monoKeith/GPS_Performance_Box/Firmware/src/monitor.cpp

/**
   The MIT License (MIT)

   Copyright (c) 2018 by ThingPulse, Daniel Eichhorn
   Copyright (c) 2018 by Fabrice Weinberg

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
   ThingPulse invests considerable time and money to develop these open source libraries.
   Please support us by buying our products (and not the clones) from
   https://thingpulse.com

*/

#include "monitor.h"

namespace monitor
{

    SSD1306Wire display = SSD1306Wire(0x3c, SDA_PIN, SCL_PIN);

    void setup()
    {
        display.init();
        display.flipScreenVertically();
    }

    void drawBootScreen()
    {
        // Clear
        display.clear();
        // Draw
        display.setFont(Roboto_Mono_Medium_18);
        display.setTextAlignment(TEXT_ALIGN_LEFT);
        display.drawString(0, 0, "GPS");
        display.setFont(Roboto_Mono_Medium_15);
        display.setTextAlignment(TEXT_ALIGN_RIGHT);
        display.drawString(128, 20, "Speedometer");
        display.setFont(ArialMT_Plain_10);
        display.setTextAlignment(TEXT_ALIGN_CENTER);
        display.drawString(64, 35, "Initializing...");
        display.setTextAlignment(TEXT_ALIGN_RIGHT);
        display.drawString(128, 50, "BY KEITH");
        // Done
        display.display();
    }

    void drawDebugScreen()
    {
        // Clear
        display.clear();

        // Clock
        display.setFont(ArialMT_Plain_16);
        display.setTextAlignment(TEXT_ALIGN_LEFT);
        display.drawString(0, 0, state::displayTime);
        // Date
        display.setFont(ArialMT_Plain_10);
        display.setTextAlignment(TEXT_ALIGN_RIGHT);
        display.drawString(128, 6, state::displayDate);
        // Speed
        display.setFont(Roboto_Mono_Medium_18);
        display.setTextAlignment(TEXT_ALIGN_RIGHT);
        display.drawString(128, 20, state::displaySpeed);
        // Location
        display.setFont(ArialMT_Plain_10);
        display.setTextAlignment(TEXT_ALIGN_CENTER);
        display.drawString(64, 42, state::displayLocation);
        // Uptime
        display.setFont(ArialMT_Plain_10);
        display.setTextAlignment(TEXT_ALIGN_LEFT);
        display.drawString(0, 54, "UPTIME:");
        display.setTextAlignment(TEXT_ALIGN_RIGHT);
        display.drawString(128, 54, String(millis()));

        // Done
        display.display();
    }

    void drawScreen()
    {
        // Clear
        display.clear();

        String msg = state::getMessage();

        if (msg.isEmpty())
        {
            // Target speed
            display.setFont(ArialMT_Plain_10);
            display.setTextAlignment(TEXT_ALIGN_LEFT);
            display.drawString(0, 0, "TARGET");
            display.setFont(ArialMT_Plain_24);
             display.drawString(0, 11, state::getTimer()->getTargetSpeed());
            // Clock
            display.setFont(ArialMT_Plain_10);
            display.setTextAlignment(TEXT_ALIGN_RIGHT);
            display.drawString(128, 0, state::displayTime);
            // Duration
            display.setFont(ArialMT_Plain_24);
            display.setTextAlignment(TEXT_ALIGN_RIGHT);
            display.drawString(128, 11, state::getTimer()->getDuration());
            // Speed
            display.setFont(ArialMT_Plain_16);
            display.setTextAlignment(TEXT_ALIGN_RIGHT);
            display.drawString(128, 36, state::displaySpeed);
            // Separate
            display.drawHorizontalLine(0, 53, 128);
            // Previous
            display.setFont(ArialMT_Plain_10);
            display.setTextAlignment(TEXT_ALIGN_LEFT);
            display.drawString(0, 54, "PREV: " + state::getTimer()->getPrevious());
            // Best
            display.setFont(ArialMT_Plain_10);
            display.setTextAlignment(TEXT_ALIGN_LEFT);
            display.drawString(64, 54, "BEST: " + state::getTimer()->getBest());
        }
        else
        {
            // Right corner: small time
            display.setFont(Roboto_Mono_Medium_15);
            display.setTextAlignment(TEXT_ALIGN_RIGHT);
            display.drawString(128, SCREEN_Y_OFFSET, state::displayTime);
            // Message
            display.setFont(Roboto_Mono_Medium_18);
            display.setTextAlignment(TEXT_ALIGN_LEFT);
            display.drawStringMaxWidth(0, 18 + SCREEN_Y_OFFSET, 128, msg);
        }

        // Done
        display.display();
    }

    void blackScreen()
    {
        // Clear
        display.clear();
        // Done
        display.display();
    }

    void refresh()
    {
        switch (state::displayMode)
        {
        case state::DisplayMode::REGULAR:
            drawScreen();
            break;

        case state::DisplayMode::DEBUG:
            drawDebugScreen();
            break;

        default:
            blackScreen();
            break;
        }
    }

}
