monoKeith/GPS_Performance_Box/Firmware/src/gps.h

#ifndef GPS_H
#define GPS_H

#include <Arduino.h>
#include <SparkFun_u-blox_GNSS_Arduino_Library.h> 
#include "config.h"
#include "state.h"

namespace gps
{
    extern void setup();
    extern void updateLocation();
    extern void updateTime();

    extern long lastTime;
};

#endif
